AmILabor/QuFabLab/AR-Quantenkoffer/ar_brick_firmware/images/pogo_pin.png

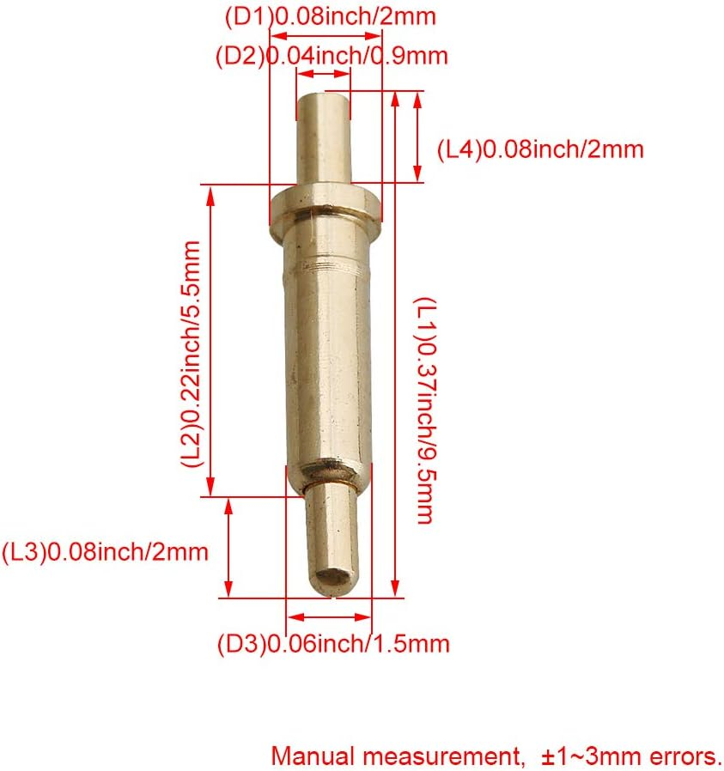
AR-Quantenkoffer/ar_brick_firmware/images/pogo_pin.png
