AmILabor/QuFabLab/hololensv2/Assets/Resources/ReadmeIMG/HAL-Sensor.jpg

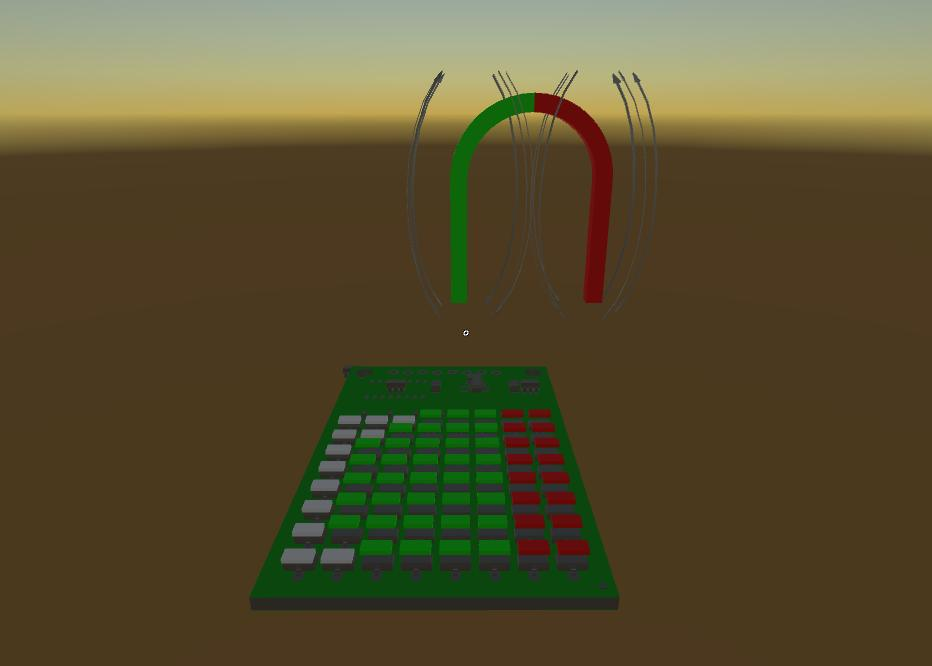
hololensv2/Assets/Resources/ReadmeIMG/HAL-Sensor.jpg
