AmILabor/QuFabLab/images/brick_bottom_with_magnets.jpeg

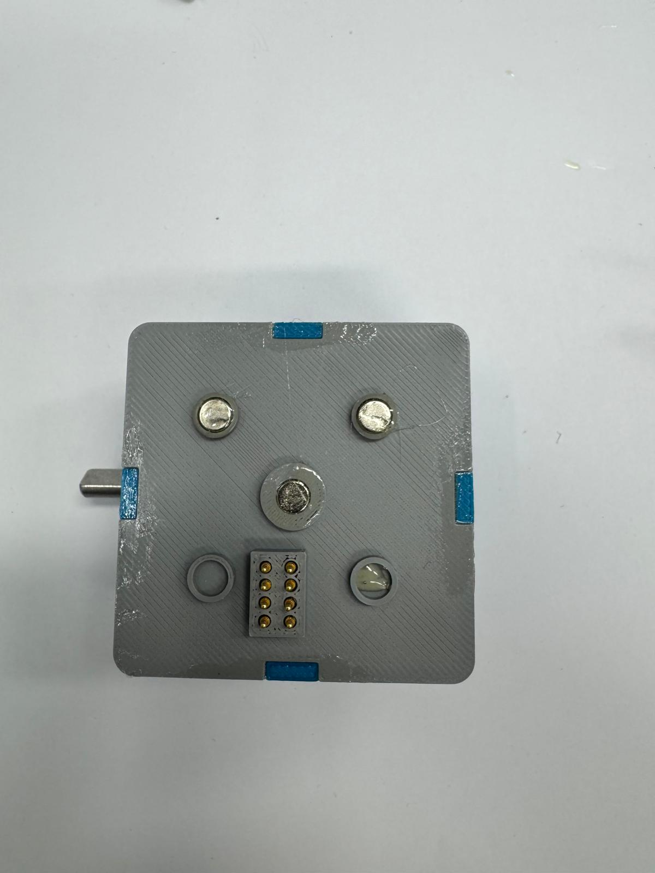
images/brick_bottom_with_magnets.jpeg
