AmILabor/QuFabLab/images/brick_bottom_with_magnets_2.jpeg

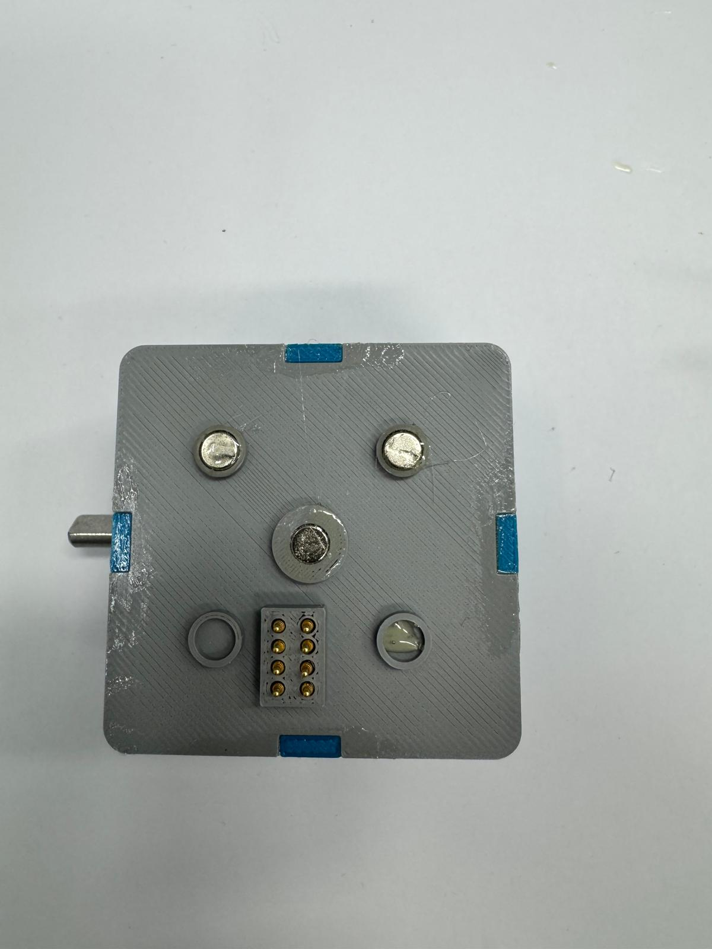
images/brick_bottom_with_magnets_2.jpeg
