AmILabor/QuFabLab/images/brick_circuit_board.jpeg

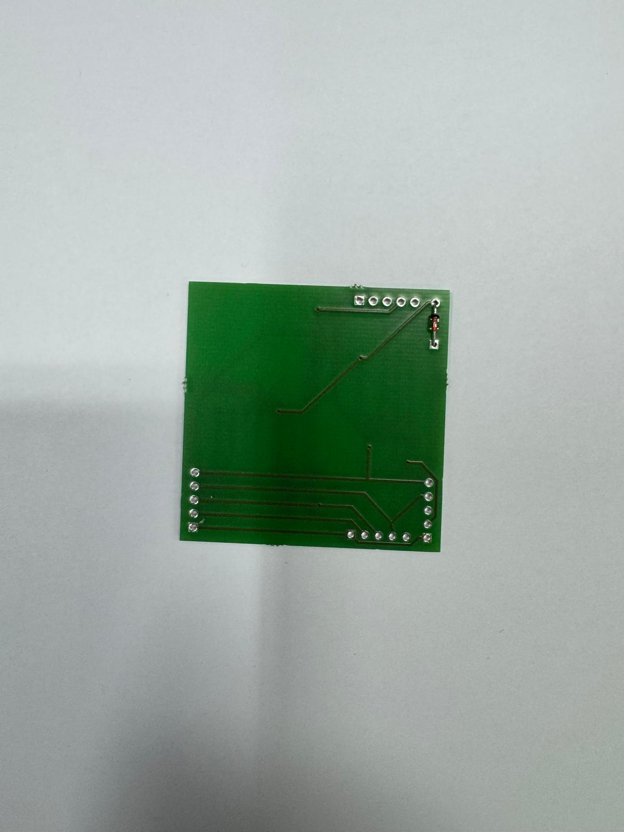
images/brick_circuit_board.jpeg
