AmILabor/QuFabLab/images/brick_circuit_board_on_brick_bottom_top_view.jpeg

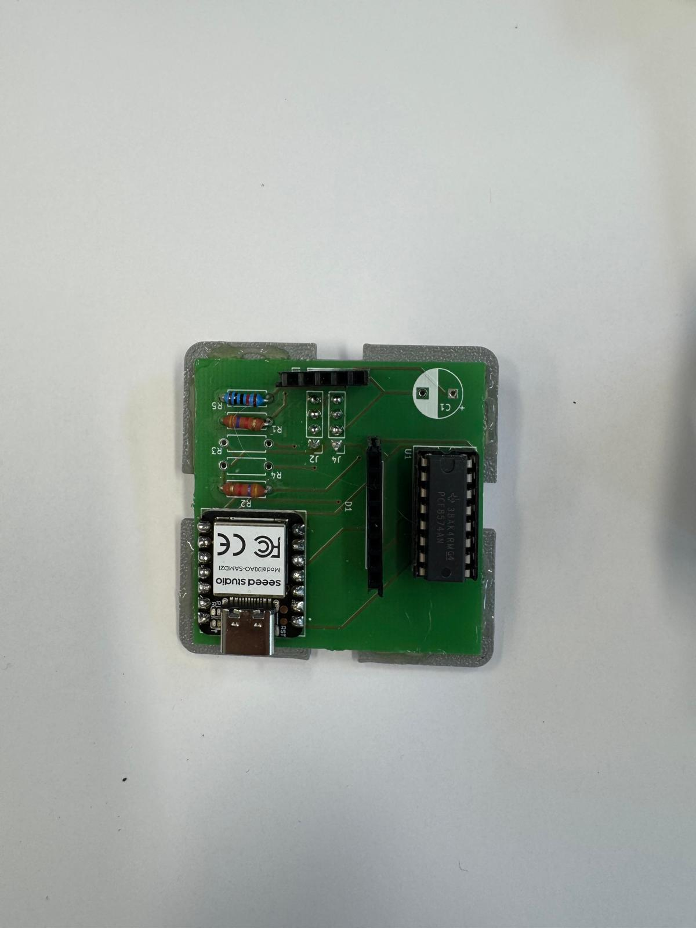
images/brick_circuit_board_on_brick_bottom_top_view.jpeg
