AmILabor/QuFabLab/images/brick_circuit_board_side_view.jpeg

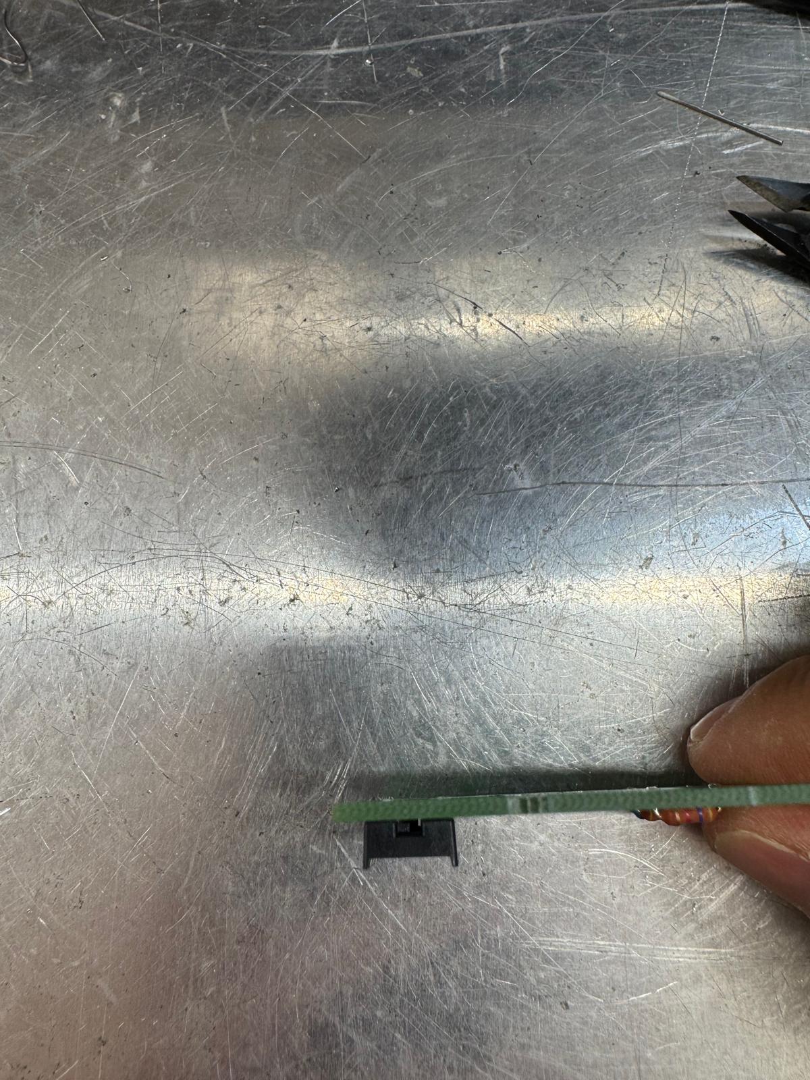
images/brick_circuit_board_side_view.jpeg
