AmILabor/QuFabLab/images/brick_circuit_board_side_view_2.jpeg

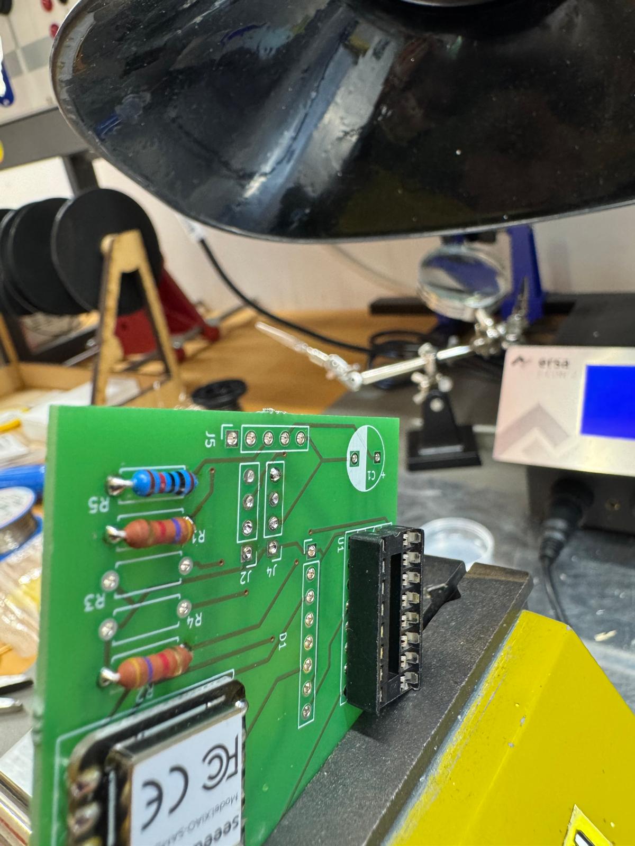
images/brick_circuit_board_side_view_2.jpeg
