AmILabor/QuFabLab/images/brick_circuit_board_side_view_3.jpeg

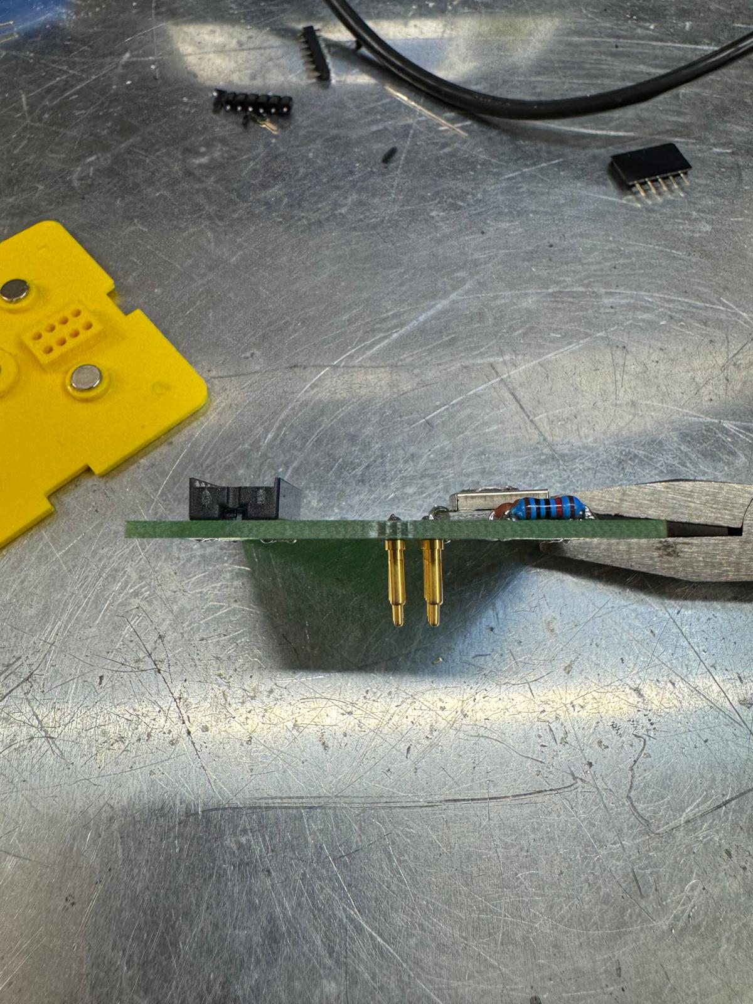
images/brick_circuit_board_side_view_3.jpeg
