AmILabor/QuFabLab/images/brick_circuit_board_side_view_pogo_pin.jpeg

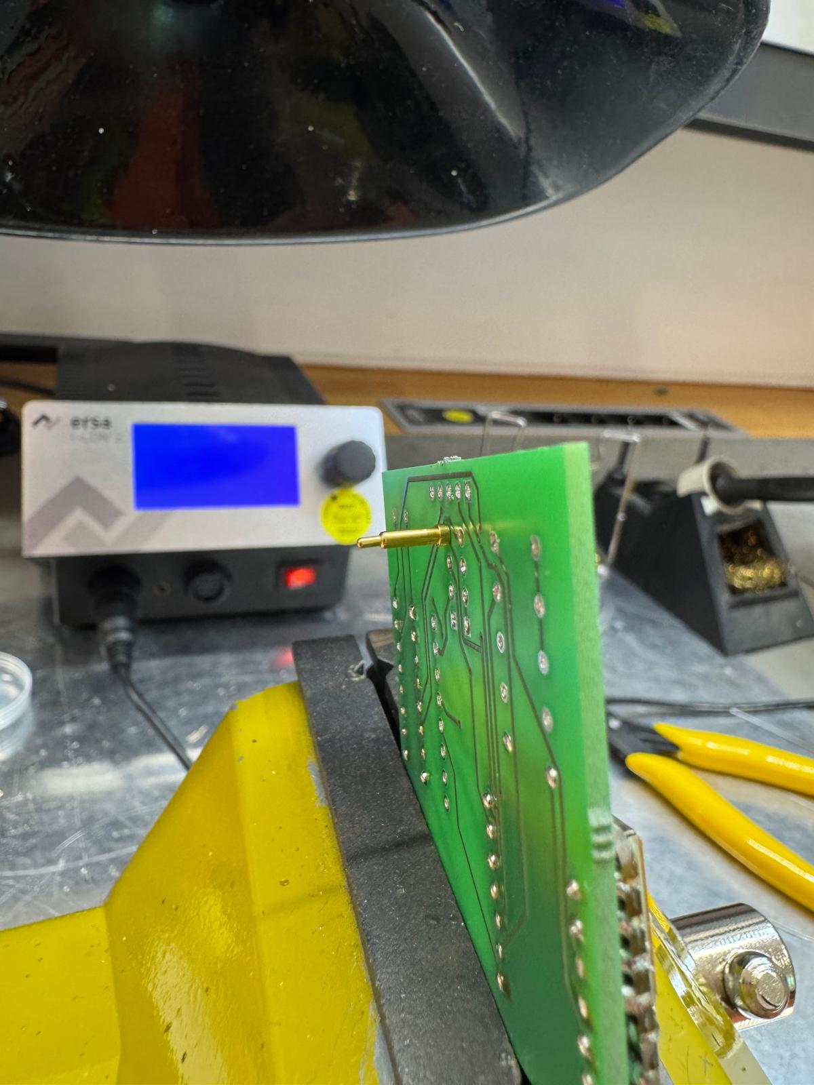
images/brick_circuit_board_side_view_pogo_pin.jpeg
