AmILabor/QuFabLab/images/brick_circuit_board_top_view_fully_equipped_2.jpeg

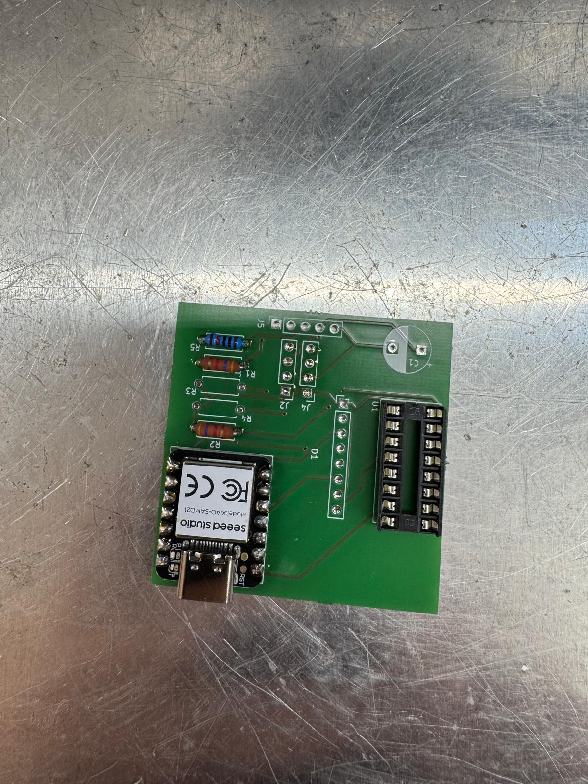
images/brick_circuit_board_top_view_fully_equipped_2.jpeg
