AmILabor/QuFabLab/images/brick_display_back.jpeg

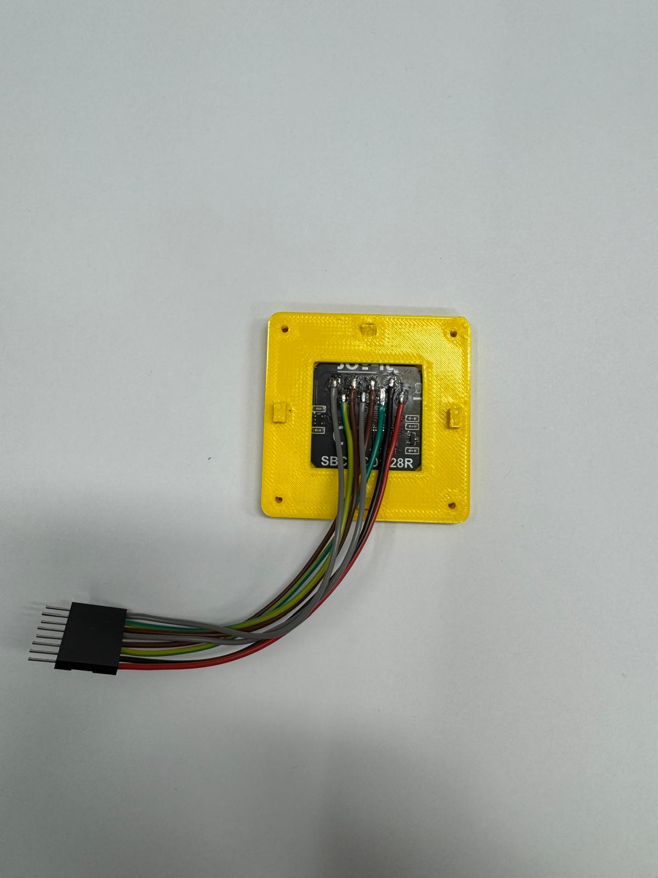
images/brick_display_back.jpeg
