AmILabor/QuFabLab/images/brick_display_top.jpeg

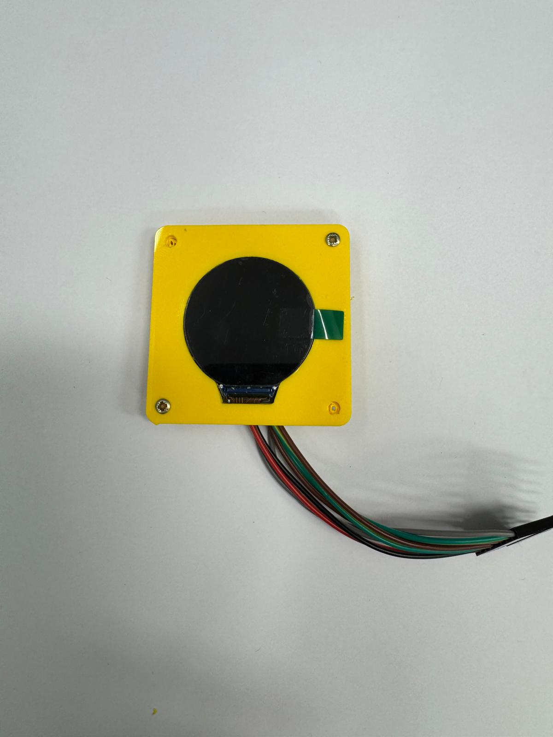
images/brick_display_top.jpeg
