AmILabor/QuFabLab/images/brick_inside.jpeg

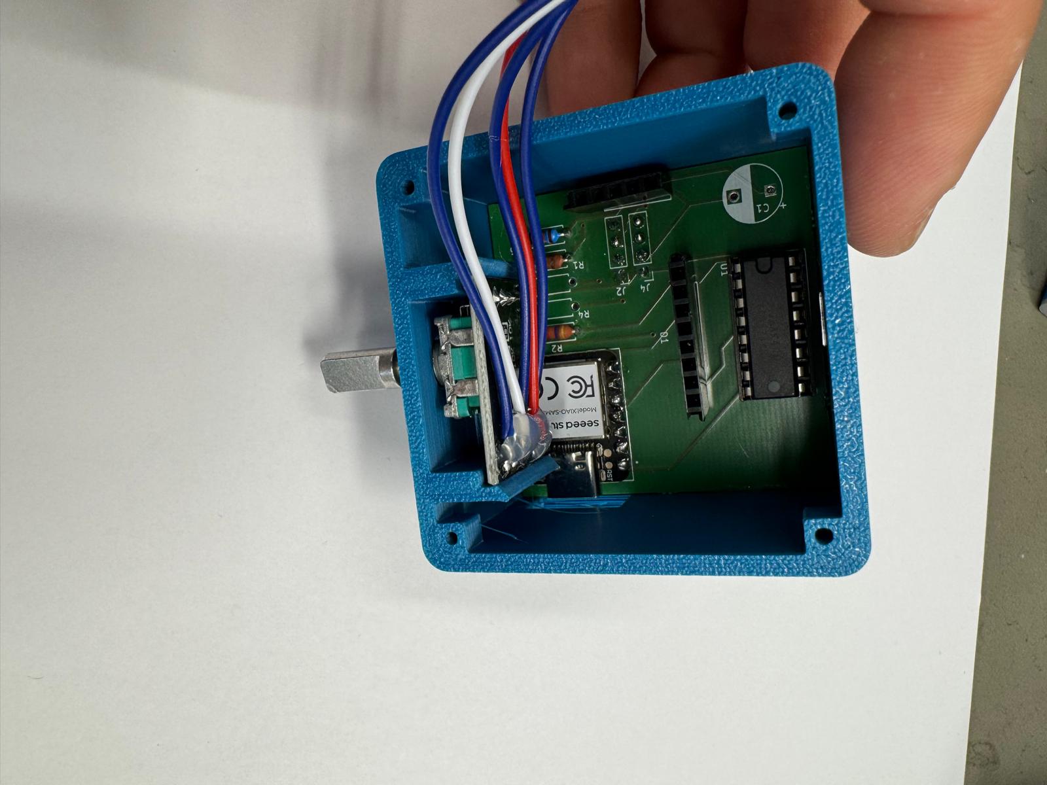
images/brick_inside.jpeg
