AmILabor/QuFabLab/images/brick_inside_2.jpeg

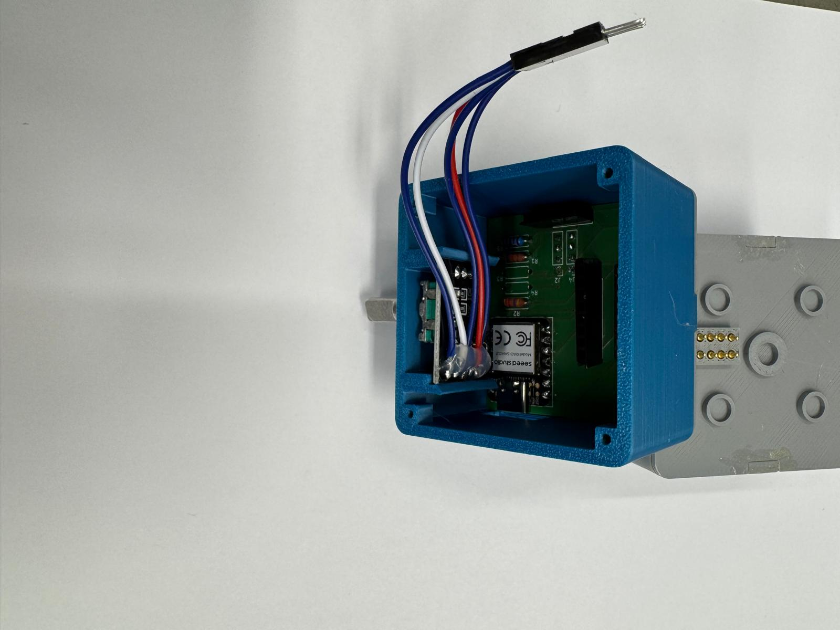
images/brick_inside_2.jpeg
