AmILabor/QuFabLab/images/brick_inside_3.jpeg

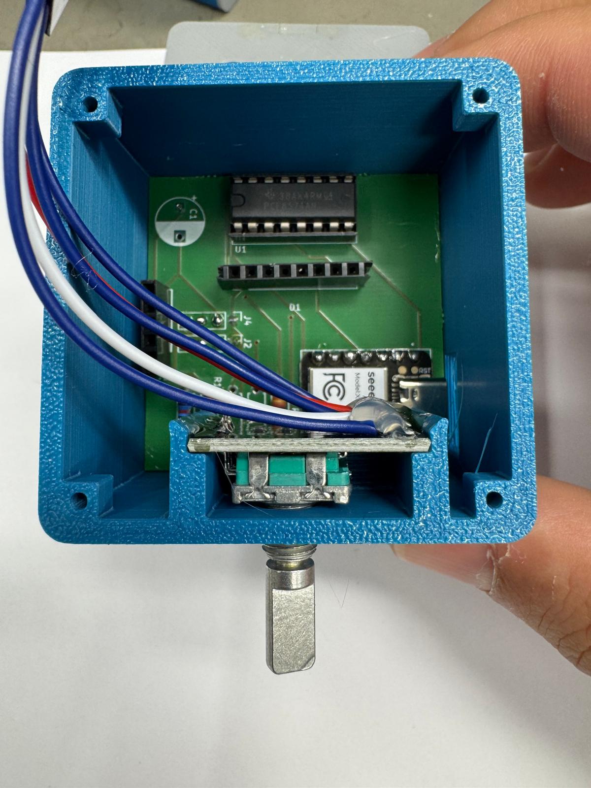
images/brick_inside_3.jpeg
