AmILabor/QuFabLab/images/circuit_board_resistor.jpeg

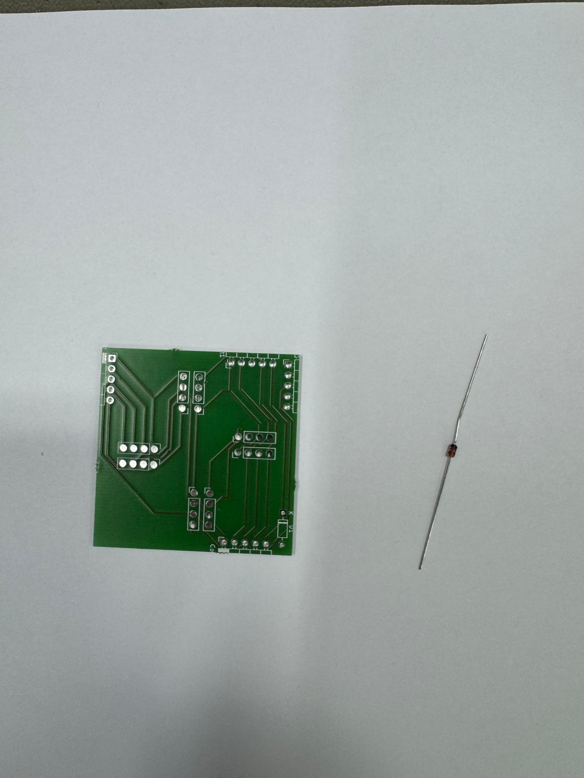
images/circuit_board_resistor.jpeg
