AmILabor/QuFabLab/images/circuit_boards_in_quboard.jpeg

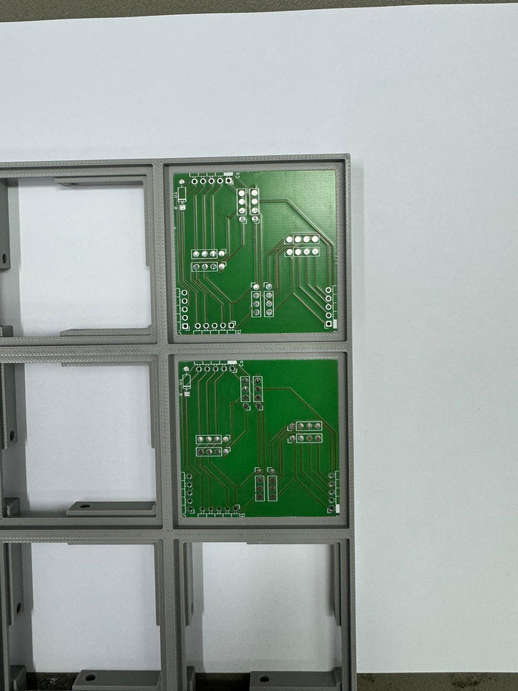
images/circuit_boards_in_quboard.jpeg
