AmILabor/QuFabLab/images/circuit_boards_in_quboard_2.jpeg

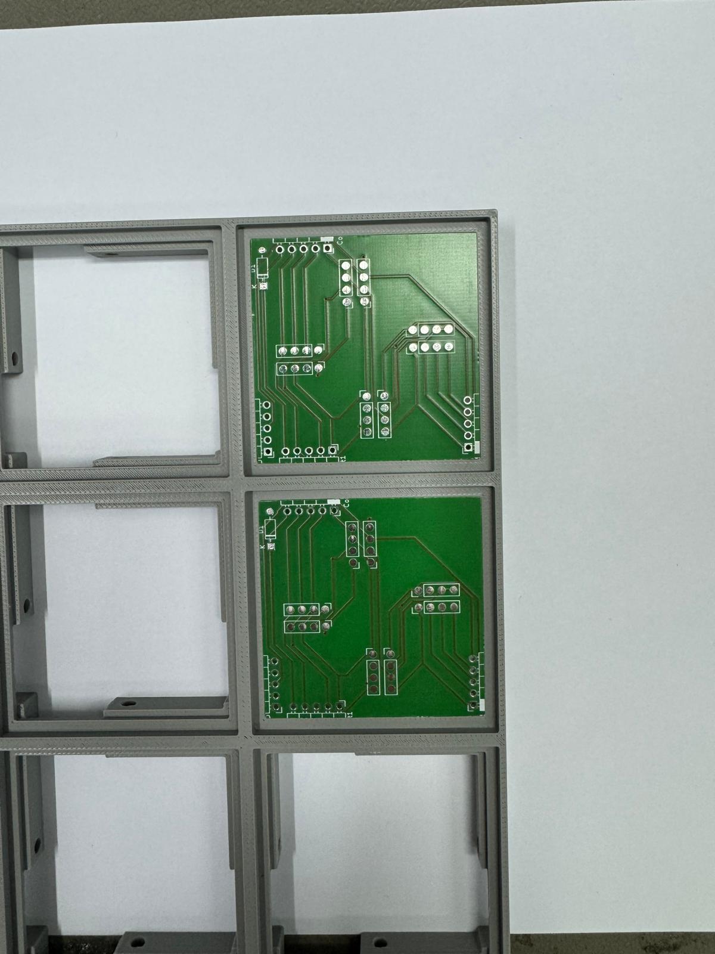
images/circuit_boards_in_quboard_2.jpeg
