AmILabor/QuFabLab/images/circuit_boards_in_quboard_with_glue.jpeg

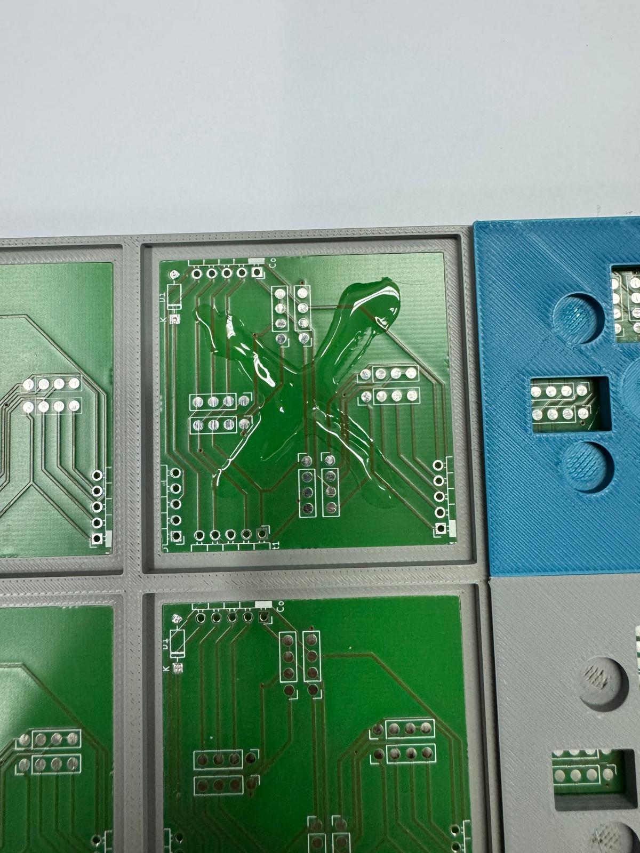
images/circuit_boards_in_quboard_with_glue.jpeg
