AmILabor/QuFabLab/images/quboard_with_magnets.jpeg

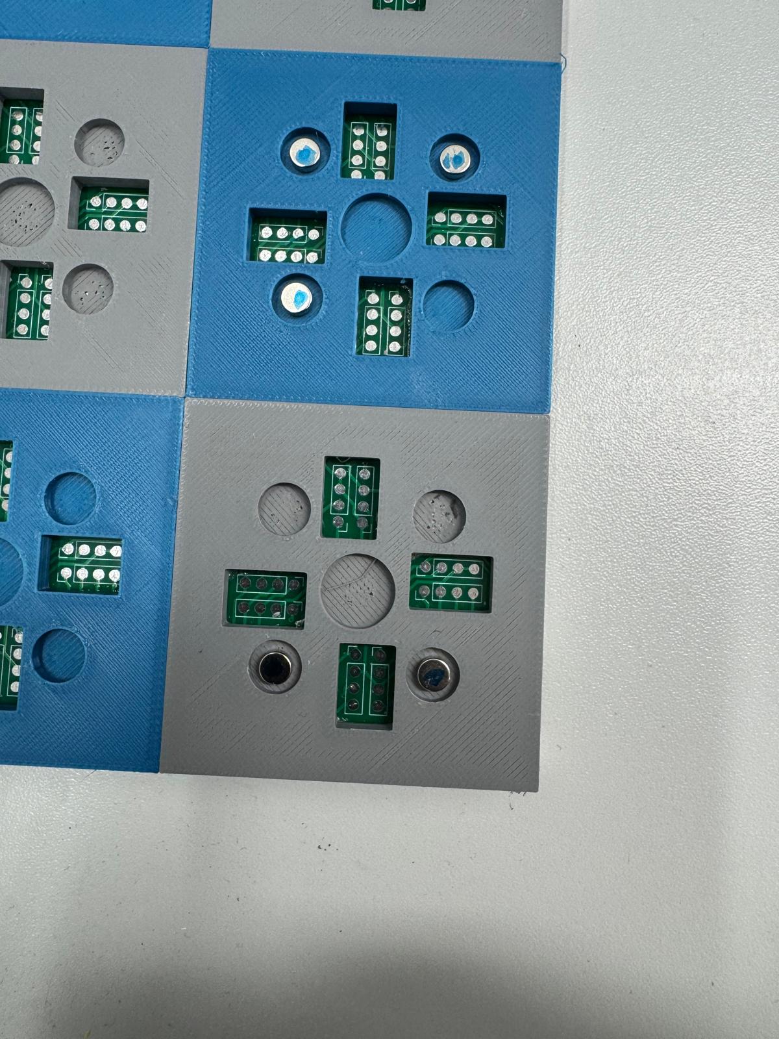
images/quboard_with_magnets.jpeg
