AmILabor/QuFabLab/moodle/PuppenApp-Docker/build_image/akte/media/uploads/wallpaper.jpg

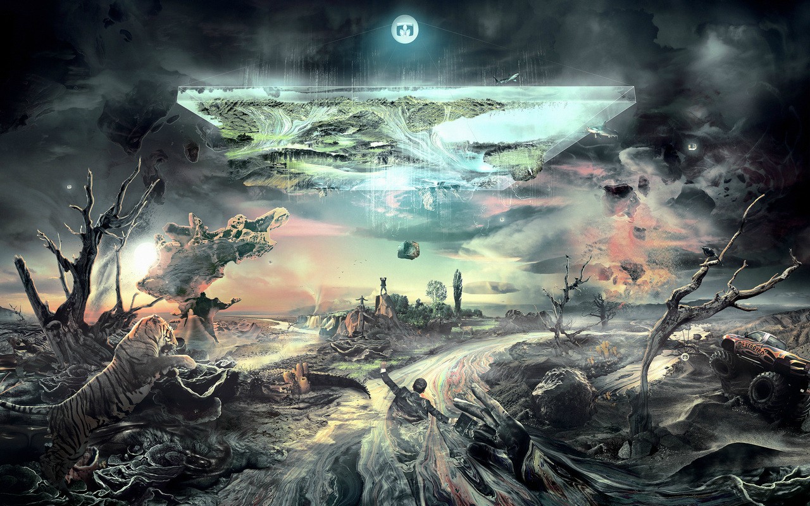
moodle/PuppenApp-Docker/build_image/akte/media/uploads/wallpaper.jpg
