AmILabor/QuFabLab/images/brick_parts_glue.jpeg

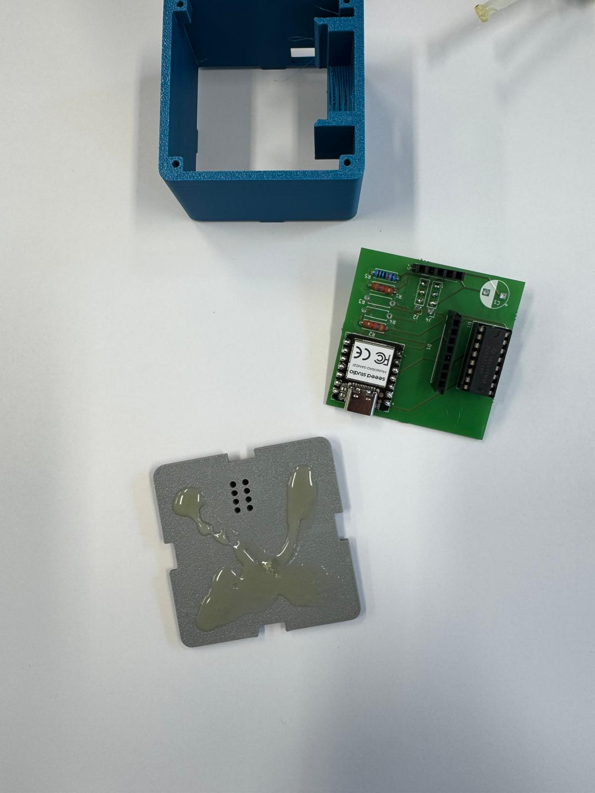
images/brick_parts_glue.jpeg
