AmILabor/QuFabLab/AR-Quantenkoffer/stls/PCB_cover_platte_0,2_reduziert.stl

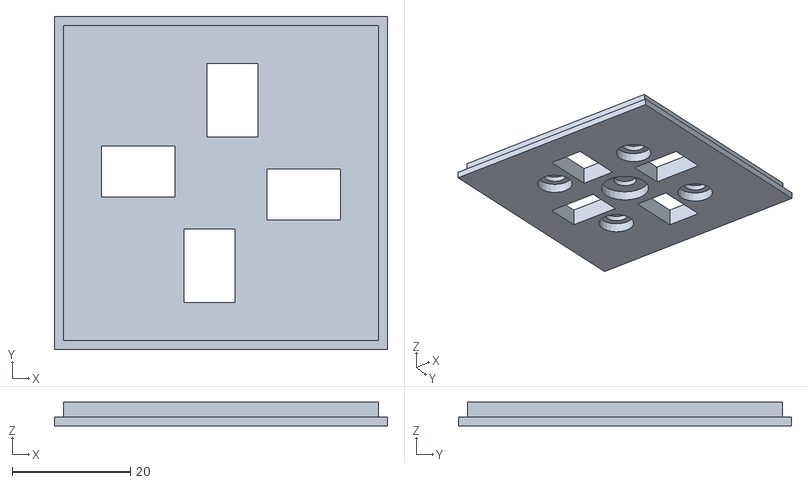
[picture p55: CAD file, 2026-07-31]
AR-Quantenkoffer/stls/PCB_cover_platte_0,2_reduziert.stl
56.3 x 56.3 x 4.00
