AmILabor/QuFabLab/AR-Quantenkoffer/stls/PCB_Kabelkanal_1.1.stl

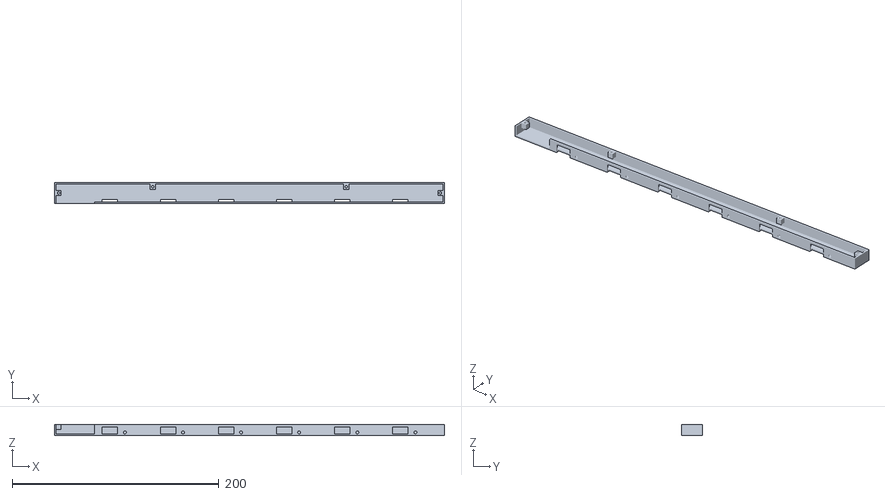
[picture p56: CAD file, 2026-07-31]
AR-Quantenkoffer/stls/PCB_Kabelkanal_1.1.stl
377.6 x 20.0 x 10.6
