AmILabor/QuFabLab/AR-Quantenkoffer/stls/PCB_Grundplatte_Platinengehäuse_V3.stl

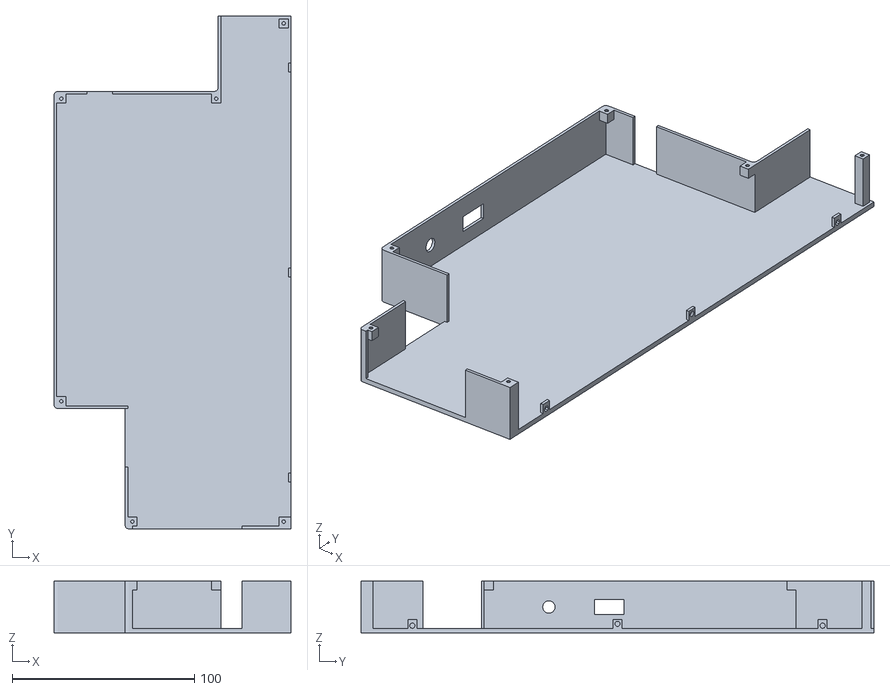
[picture p57: CAD file, 2026-07-31]
AR-Quantenkoffer/stls/PCB_Grundplatte_Platinengehäuse_V3.stl
130.0 x 281.3 x 28.5
