AmILabor/QuFabLab/AR-Quantenkoffer/stls/PCB_Qfab_Deckel.stl

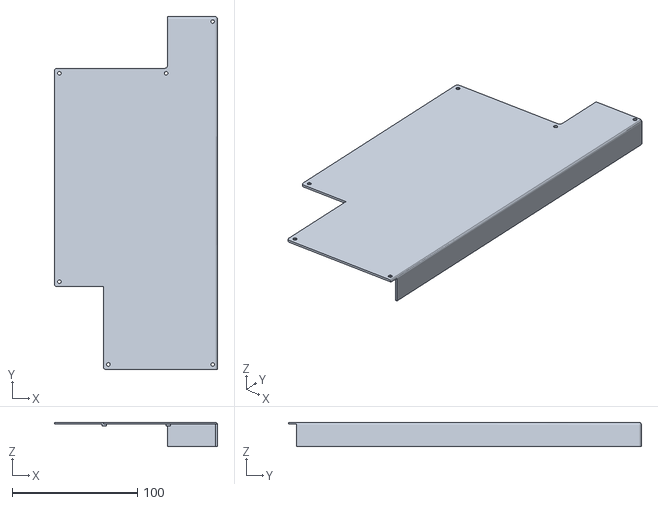
[picture p58: CAD file, 2026-07-31]
AR-Quantenkoffer/stls/PCB_Qfab_Deckel.stl
130.0 x 281.3 x 19.4
