AmILabor/QuFabLab/AR-Quantenkoffer/stls/PCB_Kabelkanaldeckel_1.1.stl

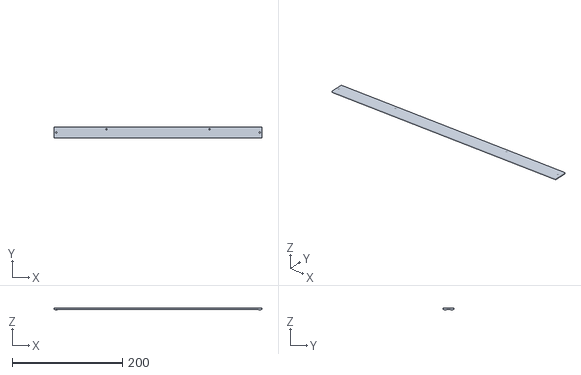
[picture p59: CAD file, 2026-07-31]
AR-Quantenkoffer/stls/PCB_Kabelkanaldeckel_1.1.stl
377.6 x 20.0 x 3.00
