AmILabor/QuFabLab/AR-Quantenkoffer/stls/pi_mount.stl

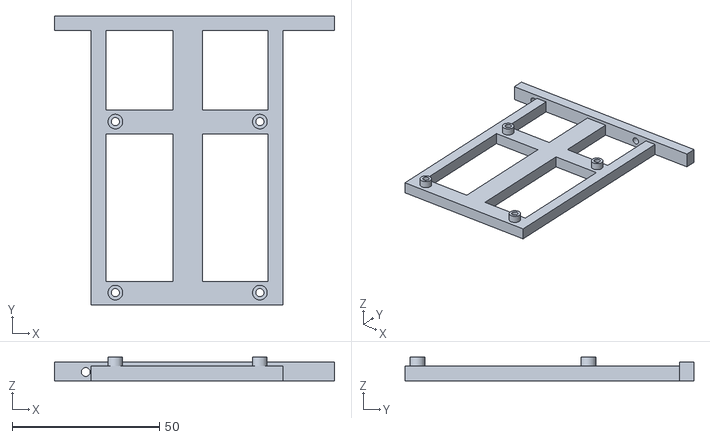
[picture p60: CAD file, 2026-02-26]
AR-Quantenkoffer/stls/pi_mount.stl
95.0 x 98.0 x 8.03
