AmILabor/QuFabLab/AR-Quantenkoffer/stls/pcb_cover_plate.stl

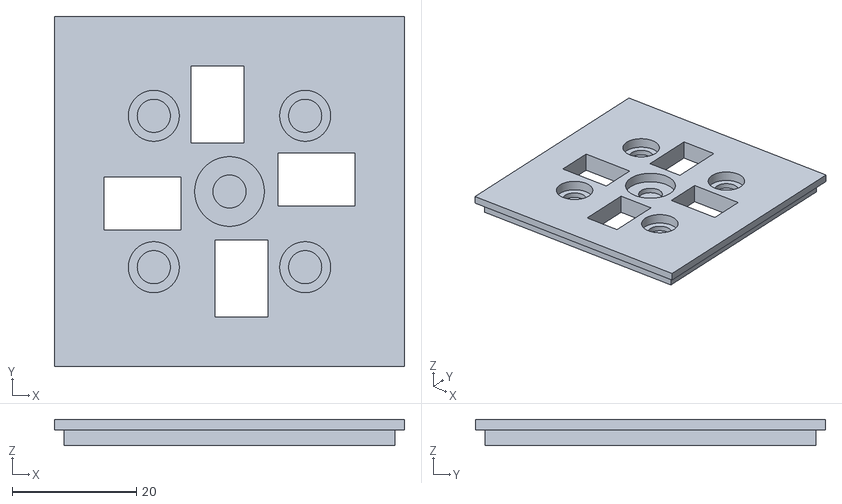
[picture p61: CAD file, 2026-02-26]
AR-Quantenkoffer/stls/pcb_cover_plate.stl
56.3 x 56.3 x 4.20
