AmILabor/QuFabLab/AR-Quantenkoffer/stls/display_fixture.stl

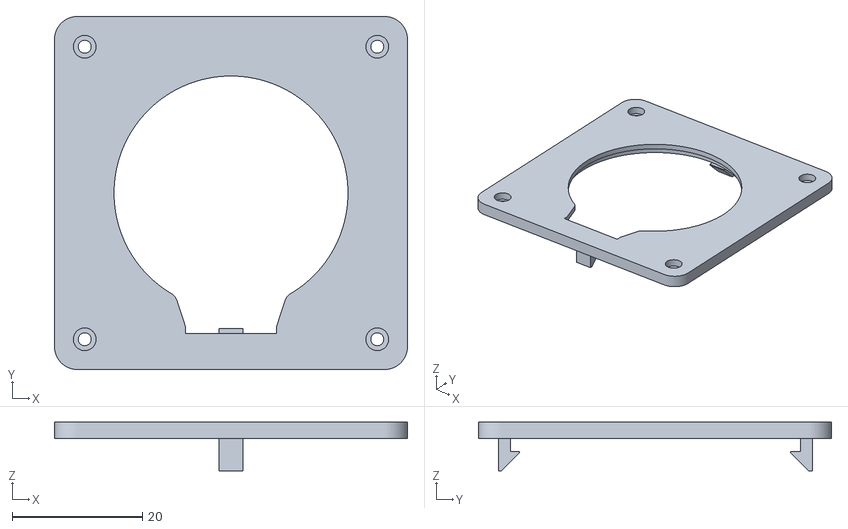
[picture p62: CAD file, 2026-02-26]
AR-Quantenkoffer/stls/display_fixture.stl
54.3 x 54.3 x 7.50
