AmILabor/QuFabLab/AR-Quantenkoffer/stls/brick_top.stl

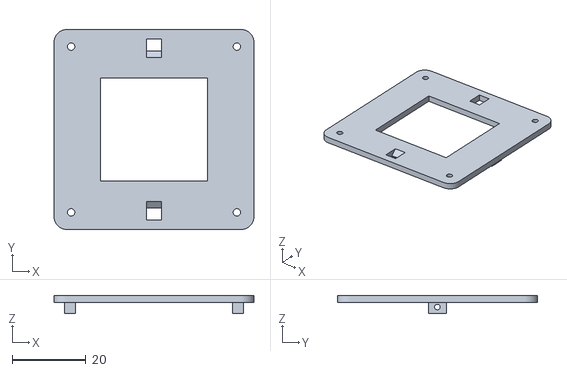
[picture p63: CAD file, 2026-02-26]
AR-Quantenkoffer/stls/brick_top.stl
54.3 x 54.3 x 5.00
