AmILabor/QuFabLab/images/quboard_wiring_view.jpeg

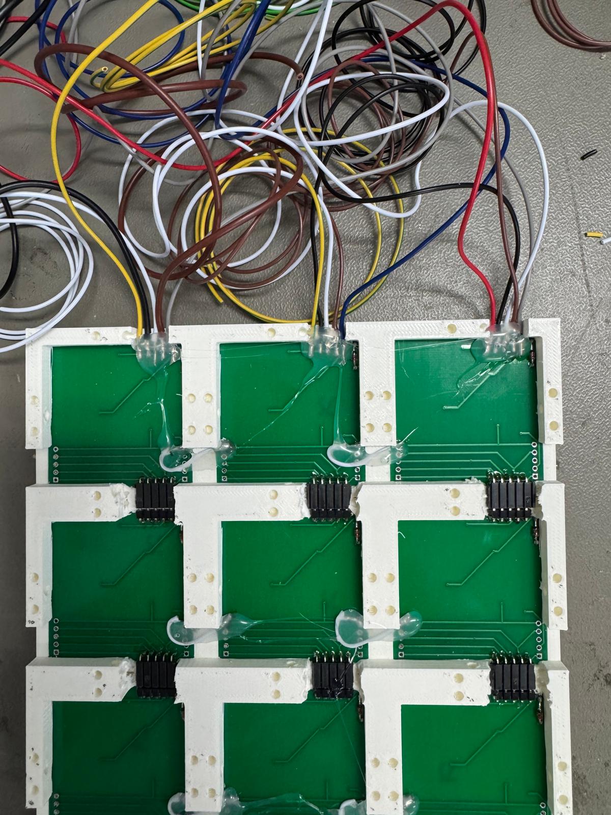
images/quboard_wiring_view.jpeg
