AmILabor/QuFabLab/moodle/PuppenApp-Docker/build_image/akte/media/220px-Wojtek_soldier_bear.png

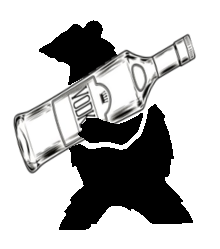
moodle/PuppenApp-Docker/build_image/akte/media/220px-Wojtek_soldier_bear.png
