AmILabor/QuFabLab/hololensv2/Assets/Resources/ReadmeIMG/DopplerExperiment.jpg

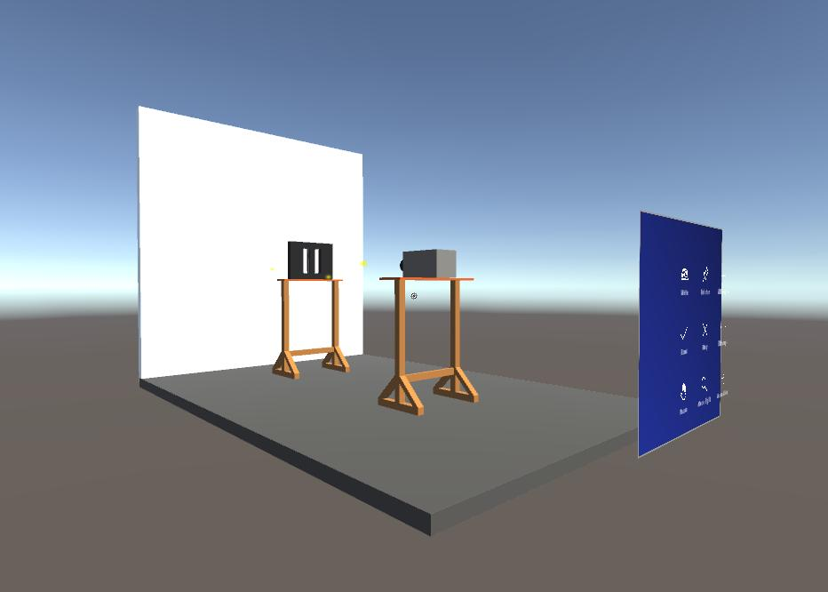
hololensv2/Assets/Resources/ReadmeIMG/DopplerExperiment.jpg
