AmILabor/QuFabLab/moodle/clex-backend/media/attachments/test.png

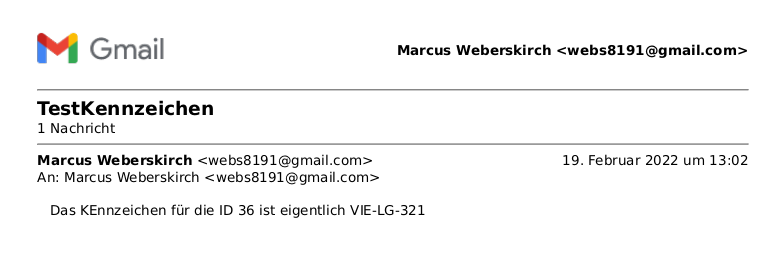
moodle/clex-backend/media/attachments/test.png
